schnippo/sgb/written/images/Devices.png

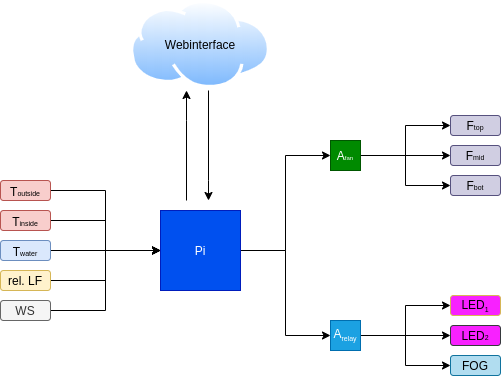
written/images/Devices.png
