schnippo/sgb/written/images/drive-download-20201018T203236Z-001/IMG_20200725_124222149_HDR.jpg

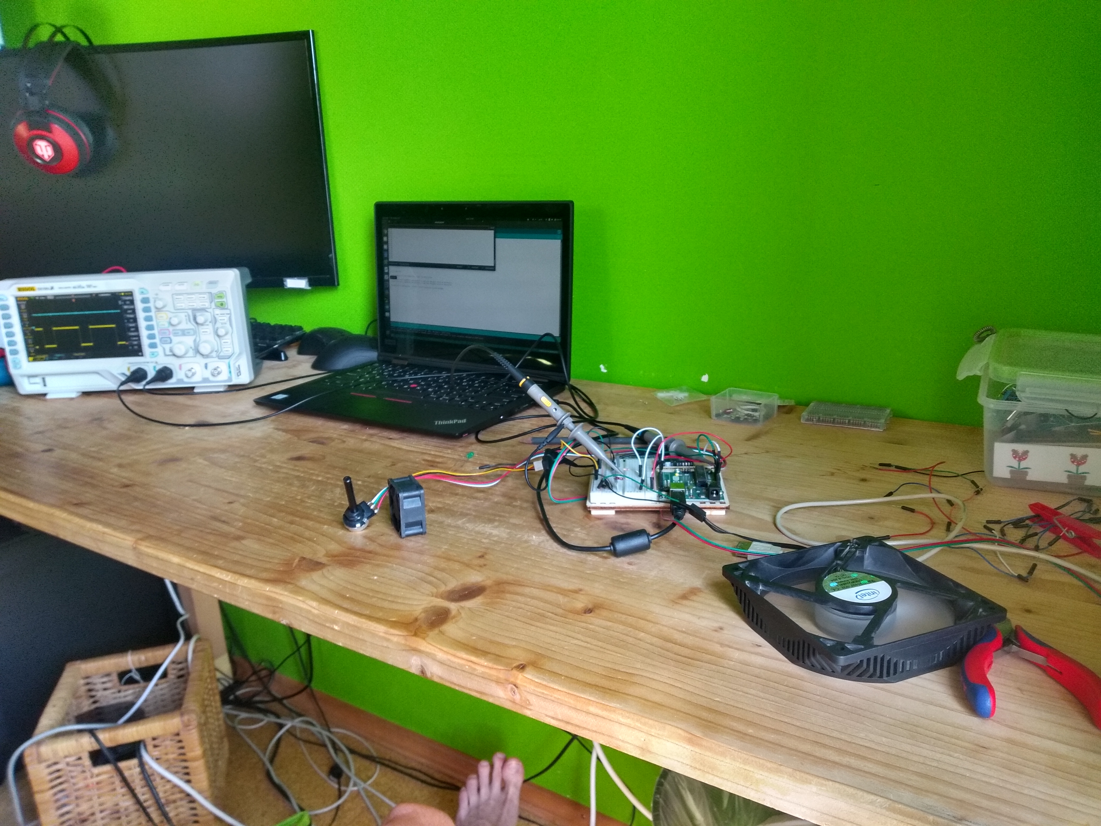
written/images/drive-download-20201018T203236Z-001/IMG_20200725_124222149_HDR.jpg
