schnippo/sgb/written/images/drive-download-20201018T203236Z-001/schaltplan.jpg

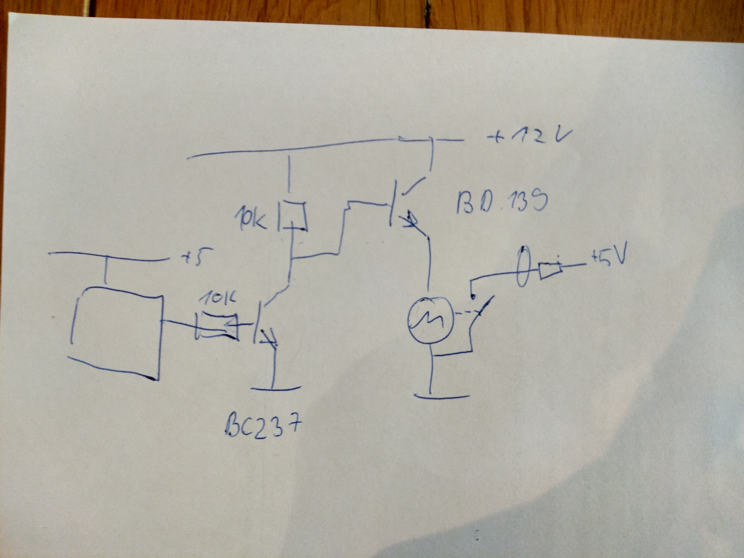
written/images/drive-download-20201018T203236Z-001/schaltplan.jpg
