schnippo/sgb/written/images/drive-download-20201018T204526Z-001/bewässerung_querschnitt.png

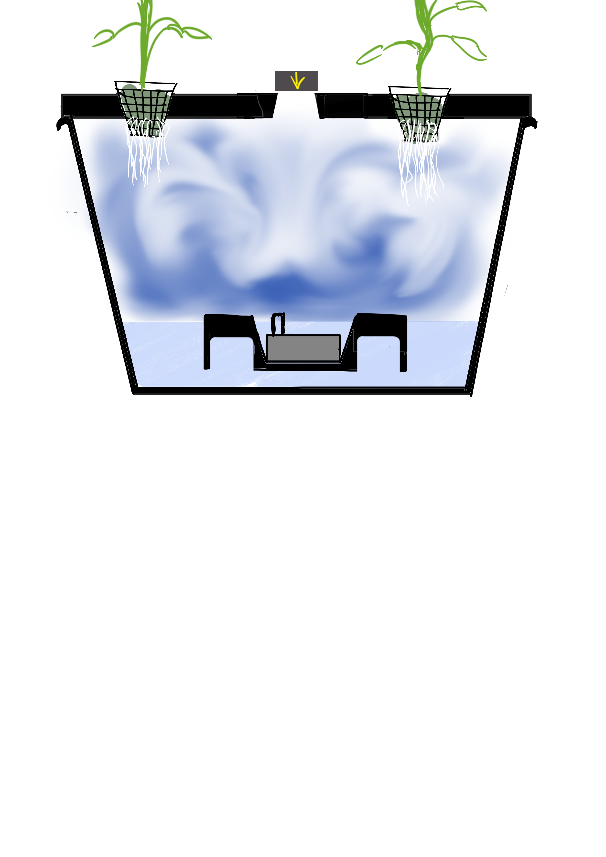
written/images/drive-download-20201018T204526Z-001/bewässerung_querschnitt.png
