schnippo/sgb/written/images/Schaltplan-pwm.png

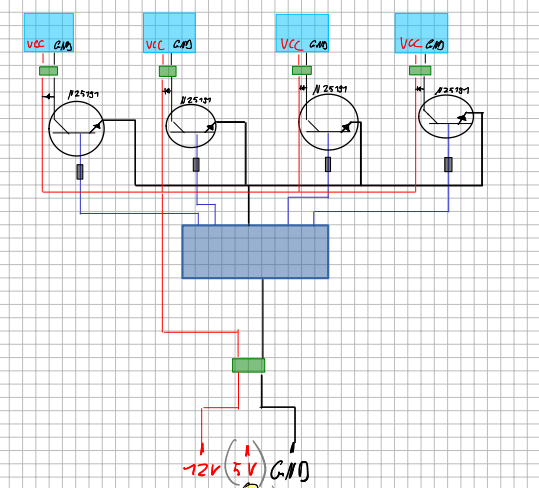
written/images/Schaltplan-pwm.png
