schnippo/sgb/written/images/schaltplan_luefter.png

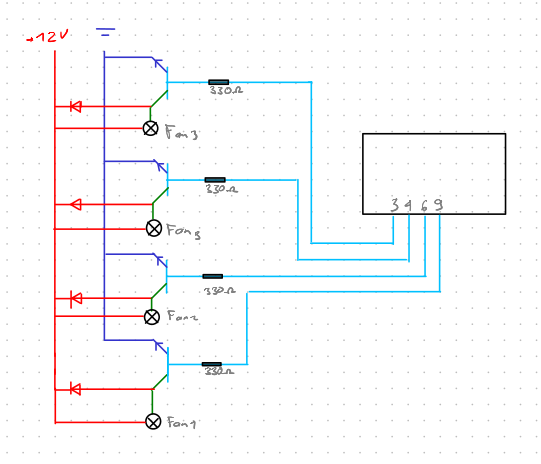
written/images/schaltplan_luefter.png
