schnippo/sgb/sensors/water/water_sensor_first/water_sensor_first.ino

#include <OneWire.h> 
#include <DallasTemperature.h>
// Data wire is plugged into pin 2 on the Arduino 
#define ONE_WIRE_BUS 2

// Setup a oneWire instance to communicate with any OneWire devices  
// (not just Maxim/Dallas temperature ICs) 
OneWire oneWire(ONE_WIRE_BUS); 


DallasTemperature sensors(&oneWire); // creates a new object that communicates with all sensors


void setup(void) 
{ 
 Serial.begin(9600); 
  
 sensors.begin();
} 
void loop(void) 
{ 
 // call sensors.requestTemperatures() to issue a global temperature 
 // request to all devices on the bus 

// Serial.print(" Requesting temperatures..."); 
 sensors.requestTemperaturesByIndex(0); // Send the command to get temperature readings 
// Serial.println("DONE"); 
/********************************************************************/
 Serial.print("Temperature is: "); 
 Serial.println(sensors.getTempCByIndex(0)); // Why "byIndex"?  
   // You can have more than one DS18B20 on the same bus.  
   // 0 refers to the first IC on the wire 
   delay(2000); 
} 
