schnippo/sgb/sensors/air/dht_sensors_first_arduino/dht_sensors_first.ino

#include <DHT.h>

#define DHT_PIN 4
#define DHTTYPE DHT22

DHT dht(DHT_PIN, DHTTYPE);


void setup() {
  // put your setup code here, to run once:
  Serial.begin(9600);
  dht.begin();
}

void loop() {
  delay(2000);
  float temp = dht.readTemperature();
  float hum = dht.readHumidity();

  if (isnan(hum) or isnan(temp)) {
    Serial.println("### Could not read from DHT sensor! ###");
  }
  Serial.print("Humidity: "); 
  Serial.print(hum);
  Serial.print(" %\t");
  Serial.print("Temperature: "); 
  Serial.print(temp);
  Serial.println(" *C ");
  
}
