schnippo/sgb/dev/power_a_random_relay.py

import serial
import random
if __name__ == '__main__':
    ser = serial.Serial('/dev/ttyACM0', 9600, timeout=1)
    ser.flush()

    while True:
        number_from_arduino = ser.read() - '0'
        if number != b'':
            if int.from_bytes(number_from_arduino, byteorder='big') == 18:
                led_number = random.randint(1,4)
                print("Button has been pressed")
                print("Sending number " + str(led_number) + " to Arduino")
                ser.write(str(led_number).encode('utf-8'))
