schnippo/sgb/written/images/drive-download-20201018T203236Z-001/IMG_20200627_165045382_HDR.jpg

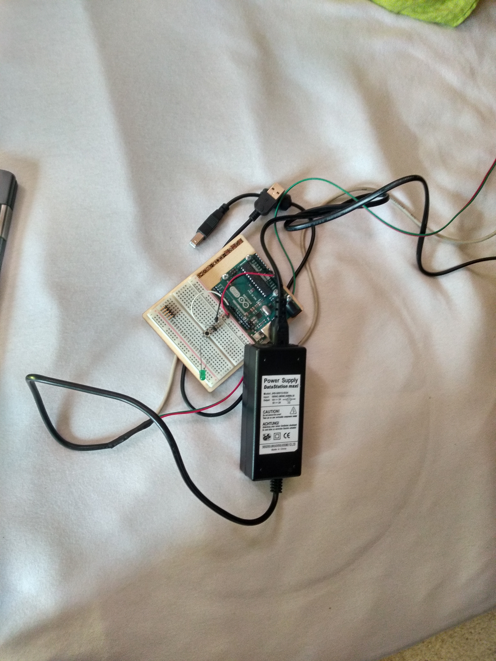
written/images/drive-download-20201018T203236Z-001/IMG_20200627_165045382_HDR.jpg
