schnippo/sgb/written/images/drive-download-20201018T204526Z-001/IMG_20201018_223816206.jpg

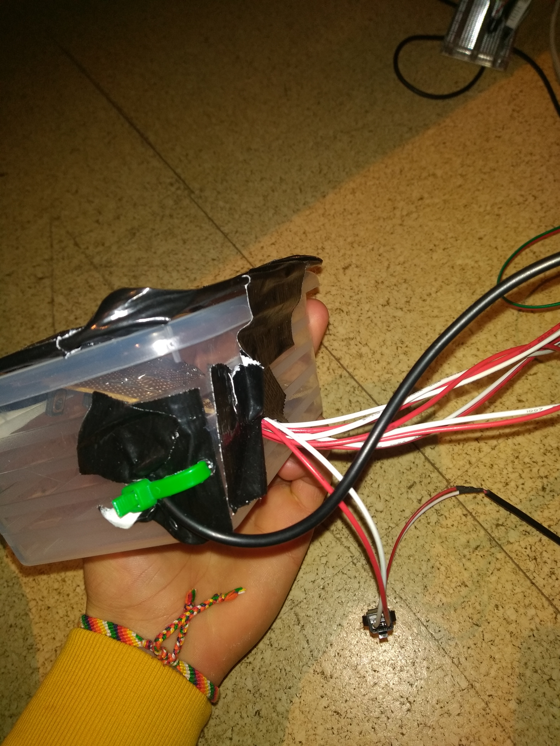
written/images/drive-download-20201018T204526Z-001/IMG_20201018_223816206.jpg
